ByteWelder/Decktility/docs/pics/battery-contacts.jpg

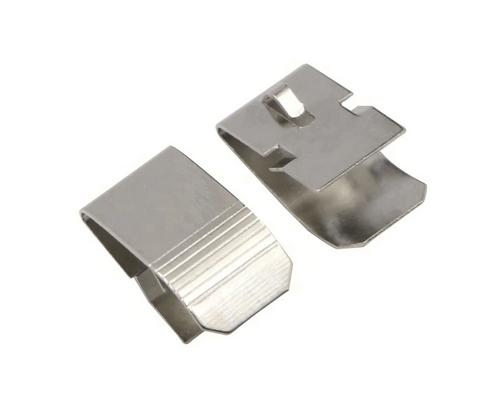
docs/pics/battery-contacts.jpg
