ByteWelder/Decktility/docs/pics/bluetooth-keyboard.jpg

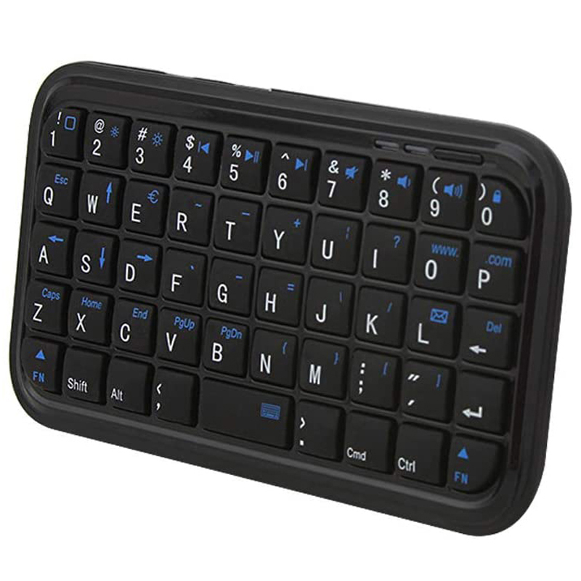
docs/pics/bluetooth-keyboard.jpg
