ByteWelder/Decktility/docs/pics/usb-c-bms.jpg

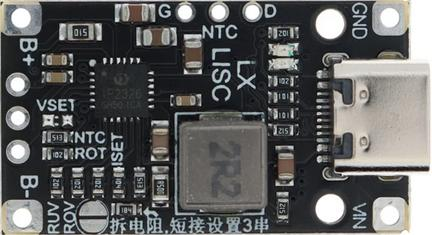
docs/pics/usb-c-bms.jpg
