ByteWelder/Decktility/docs/pics/step-down-bottom.jpg

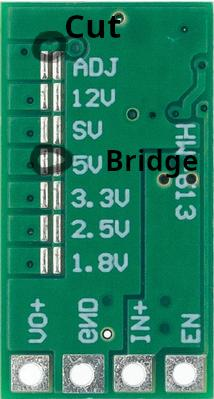
docs/pics/step-down-bottom.jpg
